casainho/temperature_humidity_sensor_eink_display/doc/prototype_01-2023.02.17.jpg

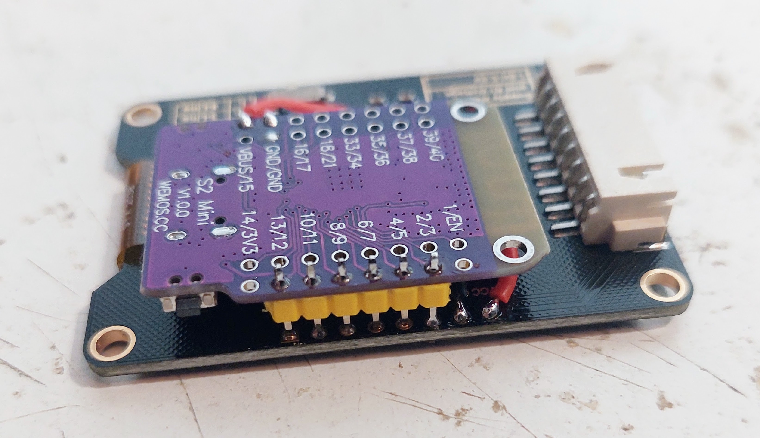
doc/prototype_01-2023.02.17.jpg
