casainho/temperature_humidity_sensor_eink_display/tools/latest_frame.png

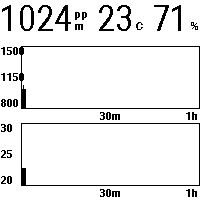
tools/latest_frame.png
