casainho/temperature_humidity_sensor_eink_display/hardware/schematic.kicad_sch

## KiCad design hardware/schematic.kicad_sch (2023-02-14)

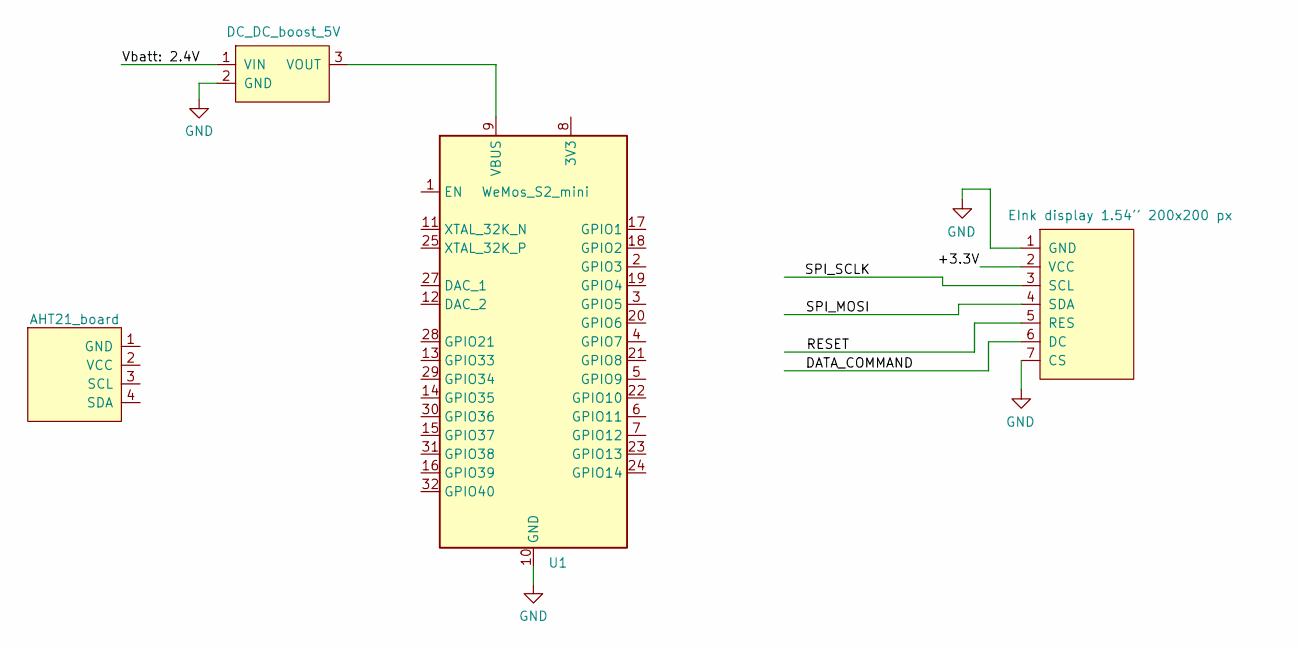
[picture p25: schematic schematic.kicad_sch]

Parts:
NA1: DC_DC_boost_5V
NA2: AHT21_board
U1: WeMos_S2_mini; WEMOS_S2_mini

Connections:
GND: NA1.2 (GND)
unnamed: NA1.3 (VOUT), U1.9 (VBUS)
unnamed: U1.10 (GND), U1.26 (GND)
Vbatt: 2.4V: NA1.1 (VIN)
